OLIMEX/iMX8MP-SOM-EVB/HARDWARE/iMX8MP-SOM-EVB-rev.b/3d/GBH2x5.stp

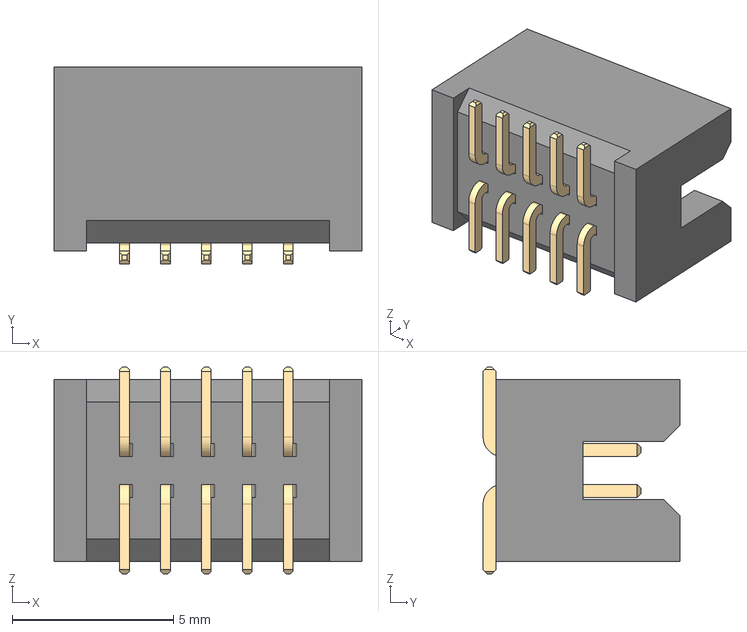
[picture p19: CAD file, 2024-05-27]
HARDWARE/iMX8MP-SOM-EVB-rev.b/3d/GBH2x5.stp
9.55 x 6.10 x 6.40 mm
