OLIMEX/iMX8MP-SOM-EVB/HARDWARE/iMX8MP-SOM-EVB-rev.b/3d/DO-214AC_SMA.step

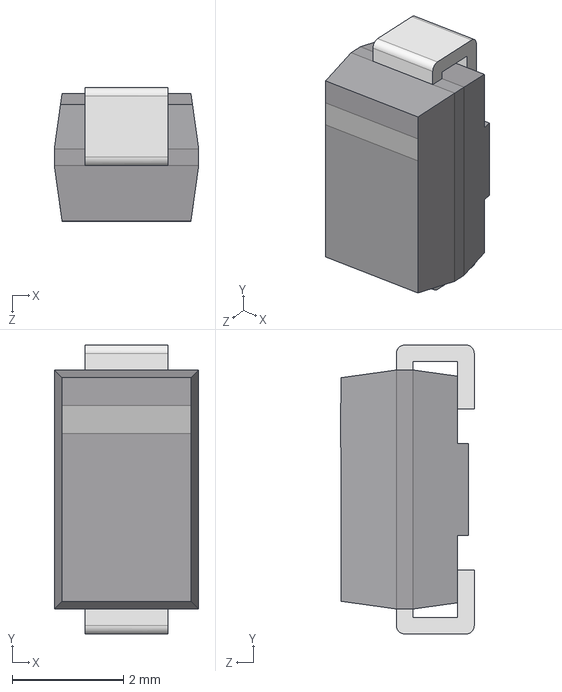
[picture p20: CAD file, 2024-05-27]
HARDWARE/iMX8MP-SOM-EVB-rev.b/3d/DO-214AC_SMA.step
2.60 x 5.20 x 2.40 mm
