OLIMEX/iMX8MP-SOM-EVB/HARDWARE/iMX8MP-SOM-EVB-rev.b/3d/SOT-23-5.step

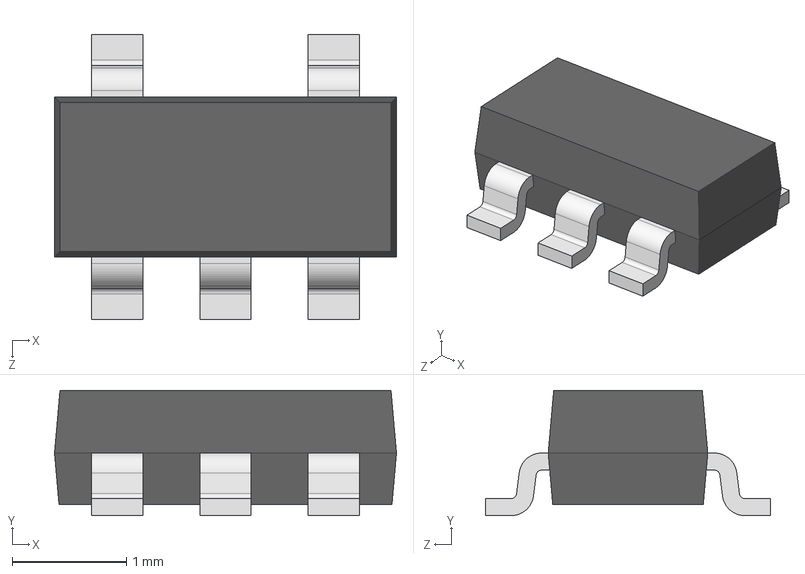
[picture p21: CAD file, 2024-05-27]
HARDWARE/iMX8MP-SOM-EVB-rev.b/3d/SOT-23-5.step
3.00 x 1.10 x 2.50 mm
