OLIMEX/iMX8MP-SOM-EVB/HARDWARE/iMX8MP-SOM-EVB-rev.b/3d/TFC-WPAPR-08---112J-TXAR-R_C_1-1.STEP

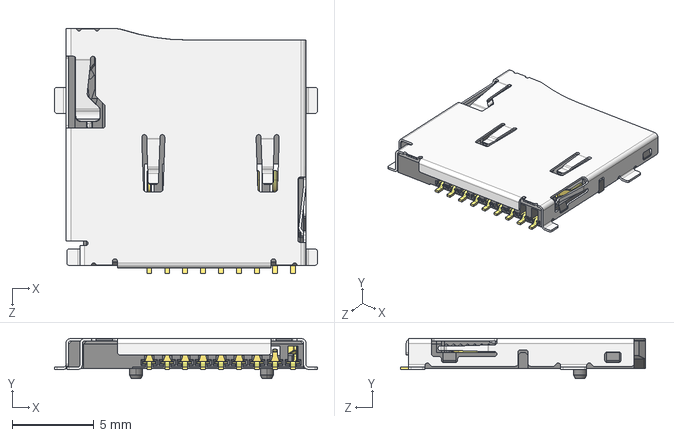
[picture p22: CAD file, 2024-05-27]
HARDWARE/iMX8MP-SOM-EVB-rev.b/3d/TFC-WPAPR-08---112J-TXAR-R_C_1-1.STEP
16.1 x 2.45 x 15.0 mm
