OLIMEX/iMX8MP-SOM-EVB/HARDWARE/iMX8MP-SOM-EVB-rev.b/3d/VSSOP8-0.5.STEP

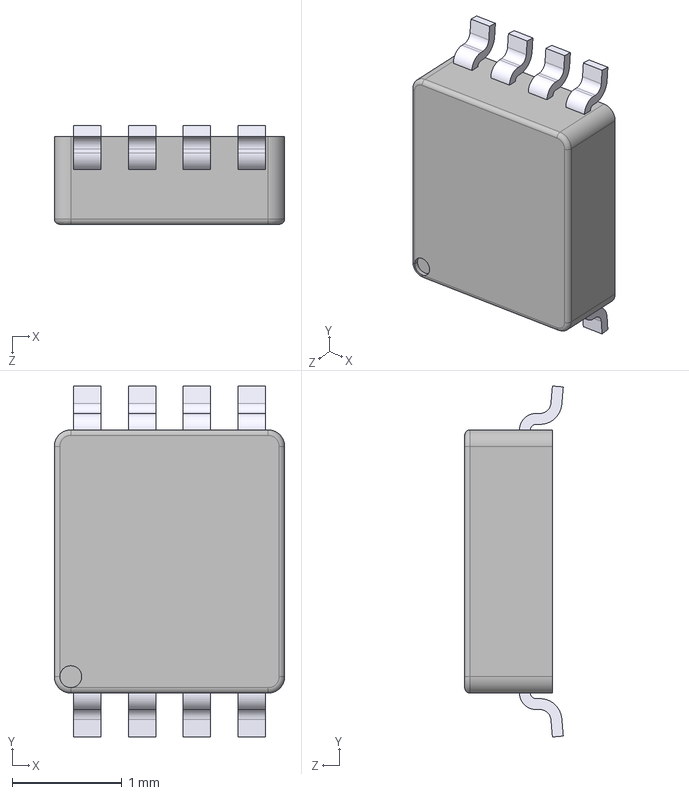
[picture p23: CAD file, 2024-05-27]
HARDWARE/iMX8MP-SOM-EVB-rev.b/3d/VSSOP8-0.5.STEP
2.10 x 3.20 x 0.9 mm
User Library-VSSOP8-1_Imported
User Library-VSSOP8-1_Imported_2
User Library-VSSOP8-1_Imported_3
User Library-VSSOP8-1_Imported_4
User Library-VSSOP8-1_Imported_5
