OLIMEX/iMX8MP-SOM-EVB/HARDWARE/iMX8MP-SOM-EVB-rev.b/3d/QFN-14_3.20x2.50mm(ASEMCC2-ZR-T3).STEP

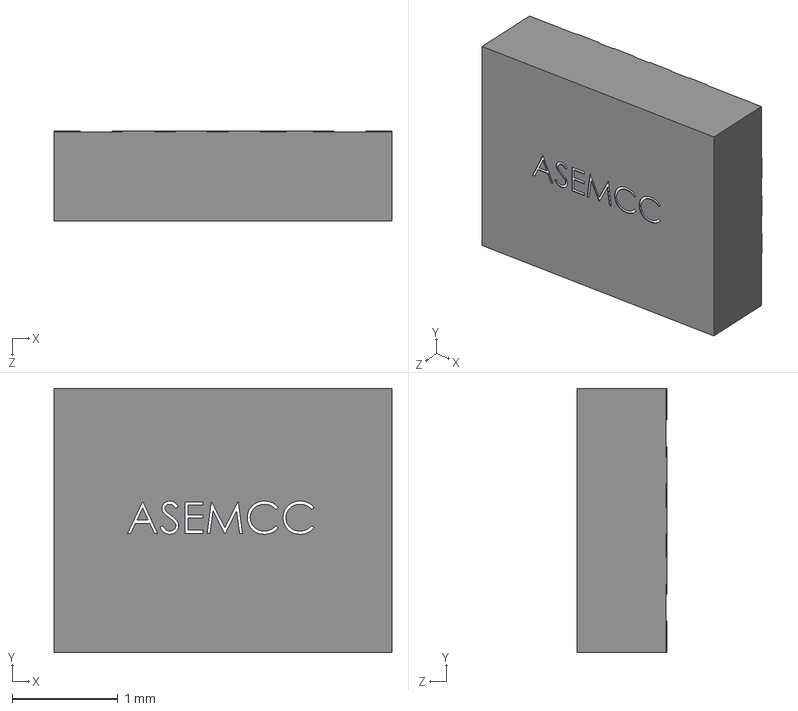
[picture p25: CAD file, 2024-05-27]
HARDWARE/iMX8MP-SOM-EVB-rev.b/3d/QFN-14_3.20x2.50mm(ASEMCC2-ZR-T3).STEP
3.20 x 2.50 x 0.85 mm
