OLIMEX/iMX8MP-SOM-EVB/HARDWARE/iMX8MP-SOM-EVB-rev.b/3d/40PinMaleSMD.stp

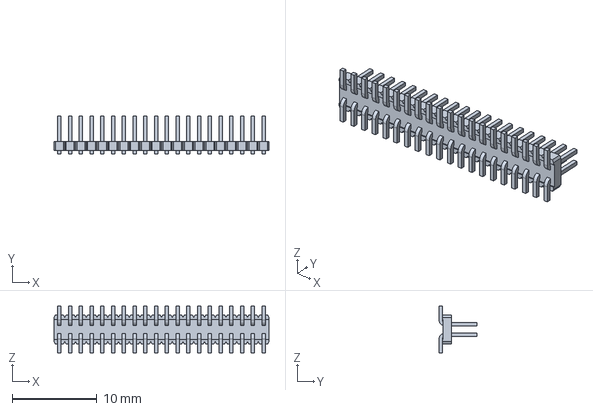
[picture p26: CAD file, 2024-05-27]
HARDWARE/iMX8MP-SOM-EVB-rev.b/3d/40PinMaleSMD.stp
25.4 x 4.50 x 5.50 mm
