OLIMEX/iMX8MP-SOM-EVB/HARDWARE/iMX8MP-SOM-EVB-rev.b/3d/dshp04ts-s.stp

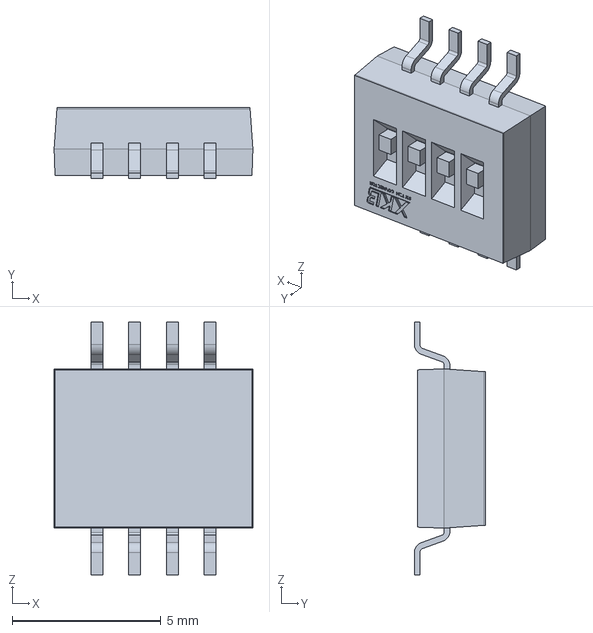
[picture p27: CAD file, 2024-05-27]
HARDWARE/iMX8MP-SOM-EVB-rev.b/3d/dshp04ts-s.stp
6.68 x 2.40 x 8.50 mm
