OLIMEX/iMX8MP-SOM-EVB/HARDWARE/iMX8MP-SOM-EVB-rev.b/3d/SO-8_150mil---SN65HVDA1050AQDRQ1.STEP

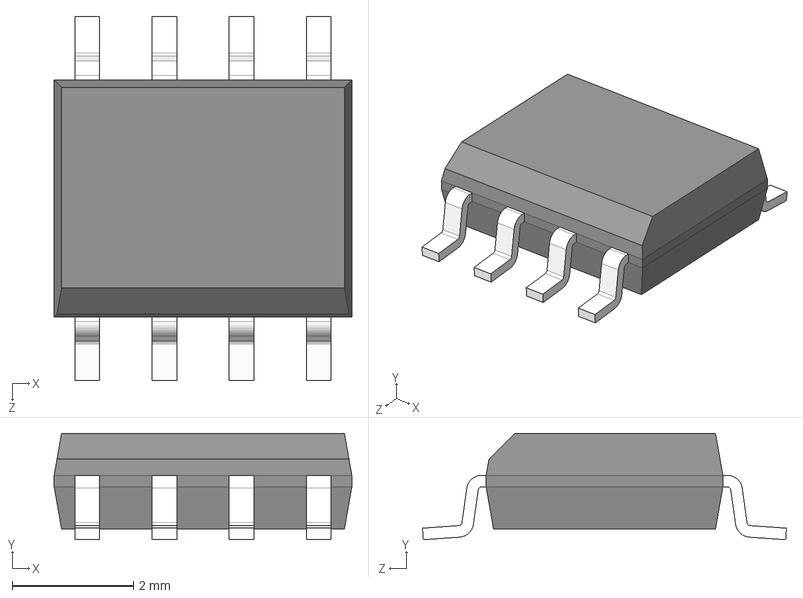
[picture p28: CAD file, 2024-05-27]
HARDWARE/iMX8MP-SOM-EVB-rev.b/3d/SO-8_150mil---SN65HVDA1050AQDRQ1.STEP
4.90 x 1.75 x 5.99 mm
