OLIMEX/iMX8MP-SOM-EVB/HARDWARE/iMX8MP-SOM-EVB-rev.b/3d/SOT-223-2.STEP

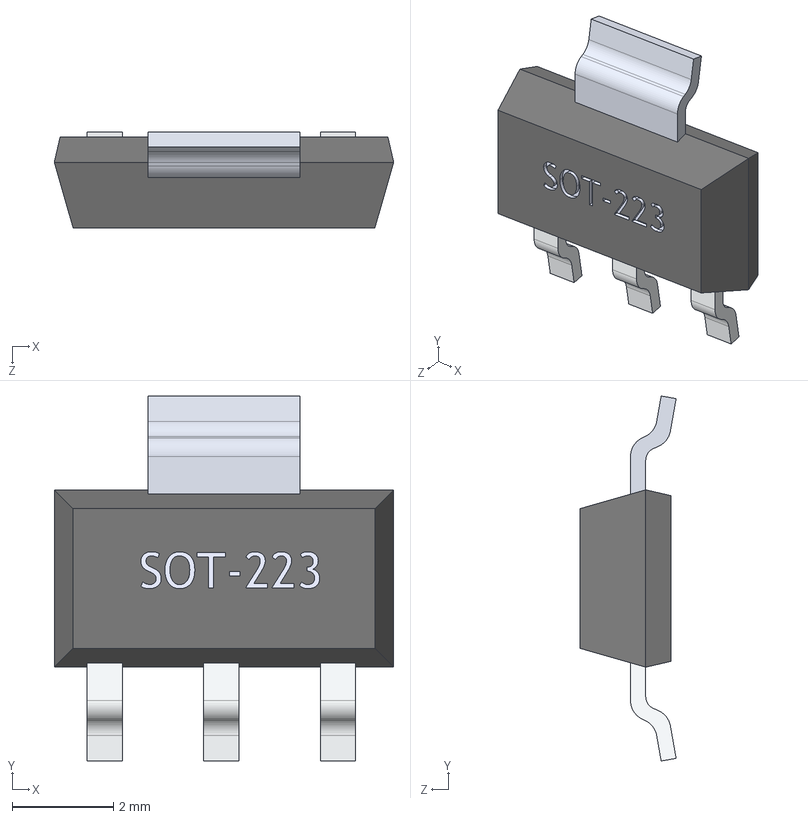
[picture p29: CAD file, 2024-05-27]
HARDWARE/iMX8MP-SOM-EVB-rev.b/3d/SOT-223-2.STEP
6.70 x 7.20 x 1.90 mm
User Library-SOT-223-2_PIN_SOT-223_2_1 x 3
User Library-SOT-223-2_SOT-223_1
User Library-SOT-223-2_PIN_SOT-223_1
