OLIMEX/iMX8MP-SOM-EVB/HARDWARE/iMX8MP-SOM-EVB-rev.b/3d/HN1x3-PinHeader_1x03_P2.54mm_Vertical.step

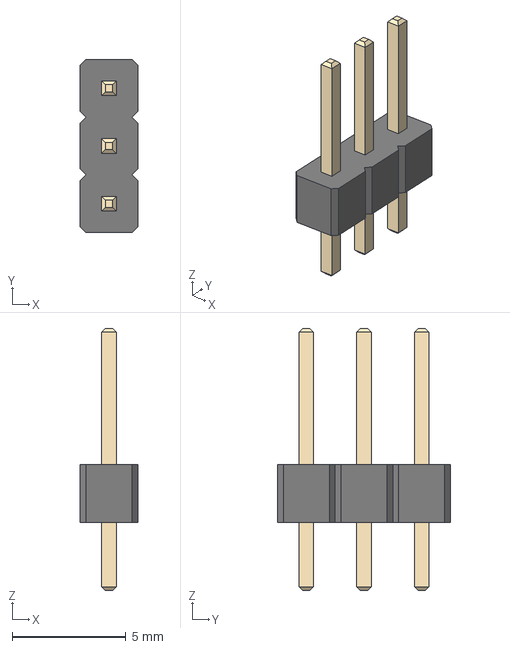
[picture p30: CAD file, 2024-05-27]
HARDWARE/iMX8MP-SOM-EVB-rev.b/3d/HN1x3-PinHeader_1x03_P2.54mm_Vertical.step
2.54 x 7.62 x 11.5 mm
