OLIMEX/iMX8MP-SOM-EVB/HARDWARE/iMX8MP-SOM-EVB-rev.b/3d/M.2(NGFF)_Series_67-Contacts.stp

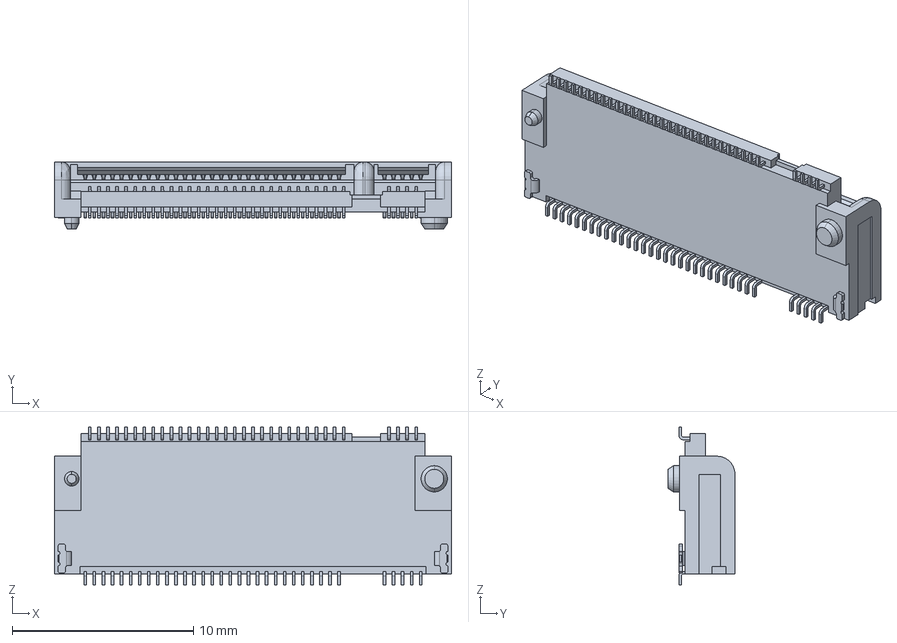
[picture p31: CAD file, 2024-05-27]
HARDWARE/iMX8MP-SOM-EVB-rev.b/3d/M.2(NGFF)_Series_67-Contacts.stp
21.9 x 3.70 x 8.70 mm
