OLIMEX/iMX8MP-SOM-EVB/HARDWARE/iMX8MP-SOM-EVB-rev.b/3d/SMD5032.STEP

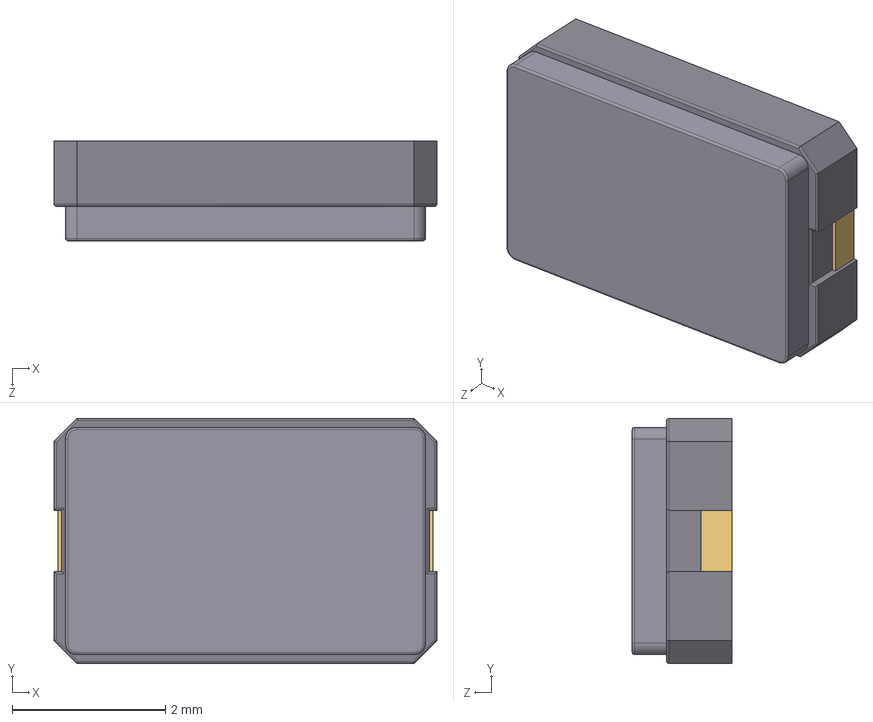
[picture p32: CAD file, 2024-05-27]
HARDWARE/iMX8MP-SOM-EVB-rev.b/3d/SMD5032.STEP
5.00 x 3.20 x 1.30 mm
User Library-ABM3-1_Fillet002
User Library-ABM3-1_Fillet001
User Library-ABM3-1_Pad001
