OLIMEX/iMX8MP-SOM-EVB/HARDWARE/iMX8MP-SOM-EVB-rev.b/3d/SLP2510P8.step

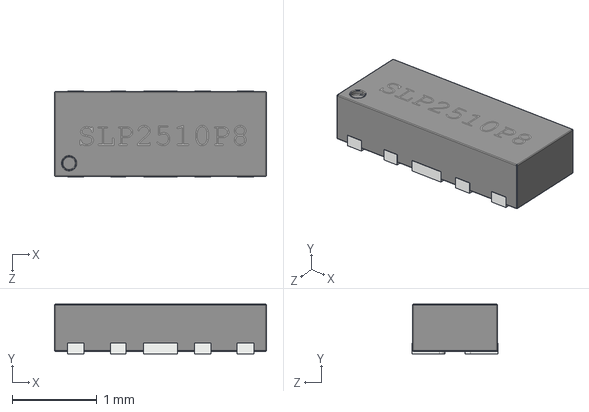
[picture p33: CAD file, 2024-05-27]
HARDWARE/iMX8MP-SOM-EVB-rev.b/3d/SLP2510P8.step
2.50 x 0.584 x 1.01 mm
