OLIMEX/iMX8MP-SOM-EVB/HARDWARE/iMX8MP-SOM-EVB-rev.b/3d/GPH2x13.stp

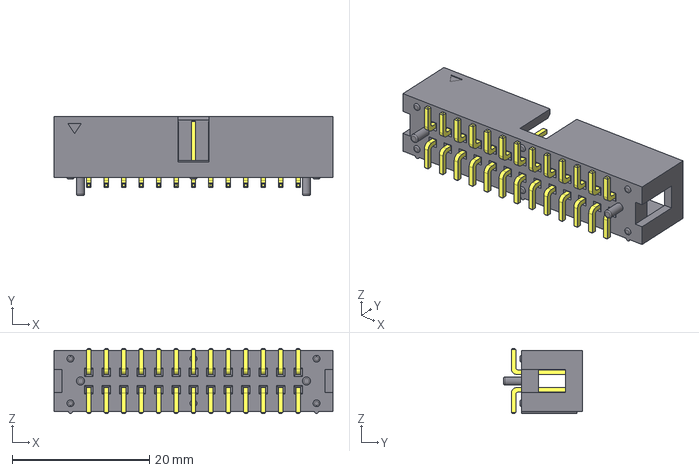
[picture p34: CAD file, 2024-05-27]
HARDWARE/iMX8MP-SOM-EVB-rev.b/3d/GPH2x13.stp
40.6 x 11.5 x 9.50 mm
GPHC204-5.81.459.5-Terminal x 26
GPHC204-13B-HSG
