OLIMEX/iMX8MP-SOM-EVB/HARDWARE/iMX8MP-SOM-EVB-rev.b/iMX8MPLUS-SOM-EVB_Rev_B.sch

## KiCad design HARDWARE/iMX8MP-SOM-EVB-rev.b/iMX8MPLUS-SOM-EVB_Rev_B.sch (2024-05-27)

Schematic: iMX8MPLUS-SOM-EVB_Rev_B.sch

Parts:
A53_DBG1: HN1x3
ARM-JTAG1: NA(HAB-VCR-010-LF); HAB-VCR-010-LF
BOOT_SWITCH1: DSHP04TS-S; DSHP04TS-S-1.27mm_Half_4_Slide
BUF1: SN74LVC1G126DBVR(SOT23-5); SOT-23-5
C1, C2, C5, C7, C8, C10, C11, C14, C15, C17, C18, C20, C23, C27, C28, C29, C30, C31, C37, C42, C43, C44, C46, C47, C48, C54, C55, C56, C57, C58, C59, C64, C65, C69, C74, C78, C79, C80, C81, C82, C83, C84, C85, C86, C87, C90, C91: 100nF/10V/10%/X7R/C0402; C_0402_5MIL_DWS
C3, C16: 1nF/2kV/10%/X7R/C1206; C_1206_5MIL_DWS_ISO
C4, C9, C12, C13, C19, C25, C38, C39, C66, C67, C72, C76, C77, C95, C96, C97: 47uF/6.3V/20%/X5R/C0805; C_0805_5MIL_DWS
C6, C21, C22, C26, C34, C35, C36, C45, C52, C53, C94: 22uF/6.3V/20%/X5R/C0603; C_0603_5MIL_DWS
C24, C49, C60, C61, C62, C63, C70, C71, C73: 10uF/6.3V/20%/X5R/C0603; C_0603_5MIL_DWS
C32, C33, C50, C51: 33pF/50V/5%/COG/C0402; C_0402_5MIL_DWS
C40, C41: 1uF/10V/10%/X5R/C0603; C_0603_5MIL_DWS
C68: NA(100nF/10V/10%/X7R/C0402); C_0402_5MIL_DWS
C75: 3.3nF/50V/10%/X5R/C0402; C_0402_5MIL_DWS
C88, C89: 10nF/50V/10%/X7R/C0402; C_0402_5MIL_DWS
C98: NA(47uF/6.3V/20%/X5R/C0805); C_0805_5MIL_DWS
CAN1, CAN2: TB3-3.5mm
CAN_T1, CAN_T2: Opened; SJ
D1, D6: 1N4007\\SMA; SMA-KA
D2, D5, D7: 1N5819S4/SOD123; SOD-123_1C-2A_KA
D3: SMBJ6.0A; DO214AA_1(K)-2(A)
D8, D9, D10: NA(1N5819S4/SOD123); SOD-123_1C-2A_KA
EXT1: B-V-26-LF(GBH254SMT-26); GBH-254-SMT-26
EXT2: P-B-V-40-LF; GBH-254-SMT-40
FET1, FET2, FET3, FET4, FET5, FET6, FET7, FET8, FET9, FET10, FET11, FET12, FET14, FET15: BSS138(SOT23-3); SOT23
FET13: IRLML6402(SOT-23); SOT23
FID1, FID2, FID3: Fiducial; Fiducial1x3
FUSE1: FSMD035; FUSE-1206
FUSE2: NA(5025); FUSE-5025
Flash_Con1: Flash_Con[DF12(3.0)-40DS-0.5V(86)]
GND1: TESTPAD; TEST_PAD40x70_SQUARE
GPIO1, GPIO2, GPIO3, GPIO5, GPIO6: MALE-PAV16X-2x20-HIGH; GPH127SMT-02X20(PA-V16X-2X20-LF)
GPIO4: MALE-PAV16X-2x10-HIGH; GPH127SMT-02X10(PA-V16X-2X10-LF)
HDMI1: HDMI-SWM-19
HEADPHONES1: PJ-3.5-365-3P(SCJ325P00XG0B02G); SCJ325P00XG0B02G
L1, L2, L3, L4, L5, L6, L7, L8, L9, L10: FB0805/600R/2A; L_0805_5MIL_DWS
LAN1, LAN2: TM211Q01FM22
M7_DBG1: HN1x3
MH1, MH2, MH3, MH4, MH5, MH6, MH7, MH8: Mounting_Hole_NPTH; Mounting_Hole_Drill-3.3mm_Clerance-7mm
MICROPHONE1: PJ-3.5-365-3P(SCJ325P00XG0B02G); SCJ325P00XG0B02G
MICRO_SD1: MICRO_SD(TFC-WPAPR-08); TFC-WPAPR-08
PWR1: T1107A(6x3,8x2,5MM)
PWRLED1: LED/Red/0603; LED_0603_KA
PWR_J1: PWRJ-2mm(YDJ-1134)
Q1, Q2: Q25MHz/20pF/20ppm/2P/5x3.2mm; HCX-4S_2Pins_5.0x3.2mm_TEST
R1, R39: 27k/R0402; R_0402_5MIL_DWS
R2, R3, R4, R43, R44: 1.5k/R0402; R_0402_5MIL_DWS
R5: 47k/R0402; R_0402_5MIL_DWS
R6, R7, R10, R13, R16, R19, R22, R23, R24, R25, R26, R27, R28, R35, R36, R49, R81: 1k/R0402; R_0402_5MIL_DWS
R8, R9, R11, R12, R17, R18, R20, R21, R40, R77, R78, R79, R102, R103, R104, R105, R124: 22R/R0402; R_0402_5MIL_DWS
R14, R83: 4.7k/R0402; R_0402_5MIL_DWS
R15, R29, R33, R37, R47, R51, R54, R58, R62, R64, R66, R67, R76, R84, R87, R106, R108: 10k/R0402; R_0402_5MIL_DWS
R30, R52, R59, R63: 330R/R0402; R_0402_5MIL_DWS
R31, R45, R46, R48, R53, R57, R61, R72, R73, R74, R85, R86, R88: NA/R0402; R_0402_5MIL_DWS
R32, R50: 12.1k/1%/R0603; R_0603_5MIL_DWS
R34, R55: 120R/R0603; R_0603_5MIL_DWS
R38: NA(22R/R0402); R_0402_5MIL_DWS
R41, R42, R82, R93, R94, R95, R96, R109, R110, R111, R112, R125: 2.2k/R0402; R_0402_5MIL_DWS
R56, R60: 120R/R1206; R_1206_5MIL_DWS
R65, R68, R69, R70, R71: NA(10k/R0402); R_0402_5MIL_DWS
R75: NA(R0402); R_0402_5MIL_DWS
R80: 10R/R0402; R_0402_5MIL_DWS
R89, R90, R91, R92, R107: 100k/R0402; R_0402_5MIL_DWS
R97: NA(2.2k/R0402); R_0402_5MIL_DWS
R98, R99, R100, R101: 49.9R/1%/R0402; R_0402_5MIL_DWS
R121, R122: NA(0R/R0402); R_0402_5MIL_DWS
RM1, RM4: RA0805_(4X0402)_4.7k; RA0805_(4X0402)_xx_BIGGEROUTPADS
RM2, RM3, RM5, RM6: RA0805_(4X0402)_22R; RA0805_(4X0402)_xx_BIGGEROUTPADS
RM7: RA0805_(4X0402)_22R; RA0805_(4X0402)_xx
RST1: T1107A(6x3,8x2,5MM)
SSD-LED1: LED/Yellow/0603; LED_0603_KA
T1: NA(LMUN2211LT1G(SOT-23)); SOT23
T2: LMUN2235LT1G(SOT-23); SOT23
TVS1, TVS2, TVS3, TVS4: ESDS314DBVR(SOT-23-5); SOT-23-5
U1, U2, U3: NA(RCLAMP0524P(SLP2510P8)); SLP2510P8_TEST
U4, U9: KSZ9031RNXIC-TR; QFN48_1DRILL(PADPITCH-0.5MM)
U5, U10: MCP2562-E/SN(SOIC-8_150mil); SOIC-8_150mil
U6, U7, U13, U14: NA(ESD5304D-10/TR); SLP2510P8_TEST
U8, U12: SY6280AAC(SOT23-5); SOT-23-5
U11: ES8388(QFN28); QFN28_EP(29)_4.076x4.076x0.9mm_Pitch_0.45mm
U15, U16, U17, U19: SN74LVC2T45DCUR(VSSOP-8); VSSOP-8_Pitch-0.50mm_Pad-0.25mm_Dimensions-2.30x2.00x1.00mm
U18: DSC557-0344FE1T(QFN-14); QFN-14_3.20x2.50x0.9mm_Pitch_0.5mm
UEXT1: P-B-V-10-LF; GBH-254-SMT-10
USB3.0_TYPE-A1, USB3.0_TYPE-A2: USB-SWZ1BL-9A-LF; USB3.0-TypeA(USB-SWZ1BL-9A-LF)
VR1, VR2: AMS1117-1.2(INDUSTRIAL); SOT223
X1: SSD-M2(APCI0107-P001A); m.2_M(NGFF-W42R-5809-LF)

Notes on the sheet:
USB3.0 HOST2
Imax=6800/Rset[4700]=1.45A
Rset
Gigabit Ethernet TSN supported
eMMC/ SPI-Flash
+5VDC ONLY!!!
Power Input
SD2_WP -> USB1_TYPEC_EN_B
MicroSD
A53 Debug
NGFF
CAN1
SAI2_RXC -> ENET_nRST
SAI2_RXFS -> ENET_nINT
Ethernet TSN
M7 Debug
eMMC
QSPIA_DQS -> VEXT_3V3_EN
QSPI Flash
USB3.0 HOST
HDMI
EXT
Audio Codec
GPIO -> CAN2_STBY
GPIO -> CAN2_RX
GPIO -> PWM4
GPIO -> PDM_CLK
GPIO -> PDM_STREAM_0
GPIO -> PDM_STREAM_1
GPIO -> PDM_STREAM_2
GPIO -> PDM_STREAM_3\CAN2_TX
GPIO -> USB1_SS_SEL
GPIO -> TCPC_nINT
GPIO -> TCPC_nINT1
GPIO -> ENET1_EVENT_IN
GPIO -> ENET1_EVENT_OUT
ENET1_nRST
ENET1_nINT
ENET1_MDC
ENET1_MDIO
ENET1_RD0
ENET1_RD1
ENET1_RD2
ENET1_RD3
GPIO -> PCIe_nWAKE
GPIO -> PCIE_nCLKREQ
GPIO -> DSI_BL_PWM
GPIO -> CSI1_SYNC
GPIO -> CSI_nRST
GPIO -> CSI2_SYNC
GPIO -> DSI_EN
GPIO -> DSI_TS_nINT
GPIO -> LVDS_EN
GPIO -> LVDS_BL_PWM
GPIO -> IOEXP_nINT
GPIO -> LVDS_TS_nINT
GPIO -> USB2_PWR_EN
GPIO -> CSI_MCLK
USB2_VBUS_3V3 is not needed for HOST only port.
====================== STRAP-IN OPTIONS - KSZ9031RNX ====================== The PHY address, PHYAD[2:0]=011 The MODE[3:0] = 1111 RGMII mode - Advertise all capabilities (10/100/1000 speed half-/full-duplex) CLK125_EN Pull-down (0) = Disable 125 MHz clock output LED_MODE Pull-up (1) = Single-LED mode
Buttons
HDMI2.0 Display with eARC RX
Gigabit Ethernet
====================== STRAP-IN OPTIONS - KSZ9031RNX ====================== The PHY address, PHYAD[2:0]=111 The MODE[3:0] = 1111 RGMII mode - Advertise all capabilities (10/100/1000 speed half-/full-duplex) CLK125_EN Pull-down (0) = Disable 125 MHz clock output LED_MODE Pull-up (1) = Single-LED mode
ENET1_TXC
ENET1_TX_CTL
ENET1_TD3
ENET1_TD2
ENET1_TD1
ENET1_TD0
ENET1_RXC
ENET1_RX_CTL
CAN Drivers
Debug UARTs
JTAG_RTCK
Debug JTAG -> Option!
I2C Address: 0x20, when AD0 is pulled down I2C Address: 0x22, when AD0 is pulled up
Audio In
Audio Out
USB3.0 HOST1
USB1_VBUS_3V3 is not needed for HOST only port.
DIR=0, direction B to A
Boot Jumpers
BOOT_MODE0, BOOT_MODE1, BOOT_MODE2, BOOT_MODE3, JTAG_MOD and POR_B must be pulled to "111111" for i.MX8M Plus to enter Boundary Scan mode.
T-Card
UEXT
Zdiff = 100 Ohm
All NC pins - Ground recommended or leave as a NC. ePAD(0) - Thermal pad, floating, not DC connected to substrate ground.
PCIe 100 MHz external oscillator and control logic
M.2(NGFF) Socket 3 – Key M
i.MX8M Plus Boot Mode
BOOT_ MODE3
BOOT_ MODE2
BOOT_ MODE1
BOOT_ MODE0
Boot Modes
Boot From Internal Fuses
USB Serial Download
USDHC3 (eMMC boot only, SD3 8‐bit)
USDHC2 (SD boot only, SD2) -> Default
NAND 8-bit single device 256 page
NAND 8-bit single device 512 page
QSPI 3B Read
QSPI Hyperflash 3.3V
ecSPI Boot
Reserved
Fiducials
Mounting Holes
Extensions
EVB to SOM - Interconnecting connectors
Almost all signals have got voltage level of 1.8V!
